circinusX1/exi-ccw/3d/EPTA-BACK.png

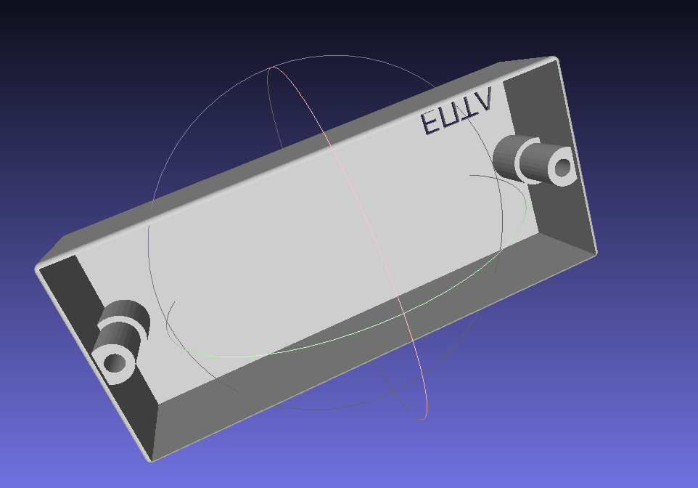
3d/EPTA-BACK.png
