circinusX1/exi-ccw/3d/EPTA-FRONT.png

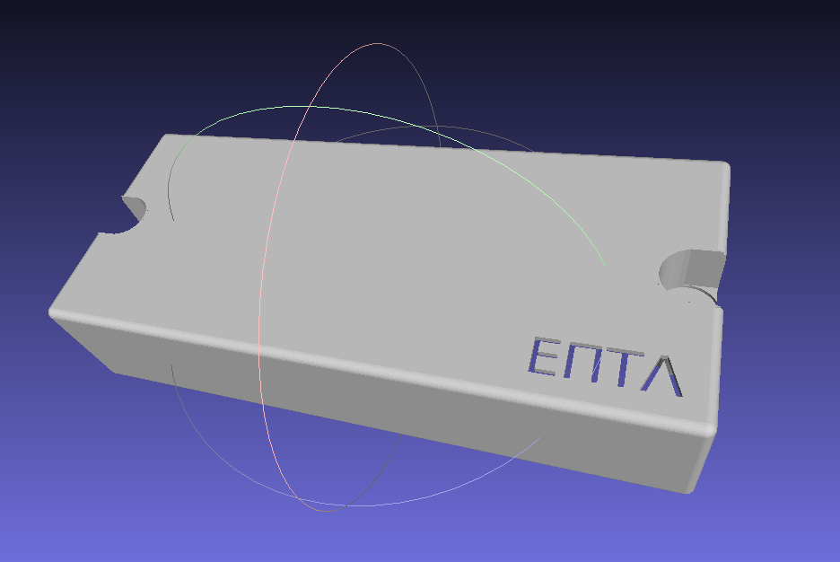
3d/EPTA-FRONT.png
