circinusX1/exi-ccw/3d/EXI-BACK.png

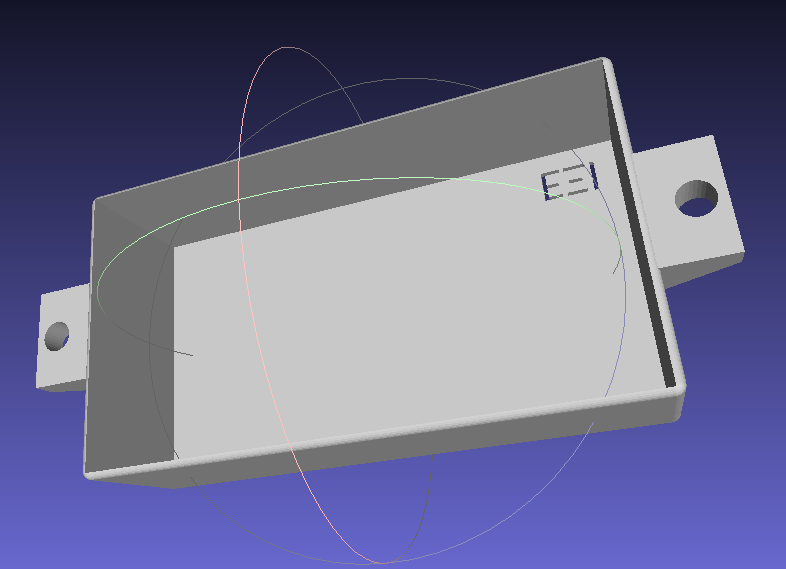
3d/EXI-BACK.png
