circinusX1/exi-ccw/3d/EXI-EPTA-CURA.png

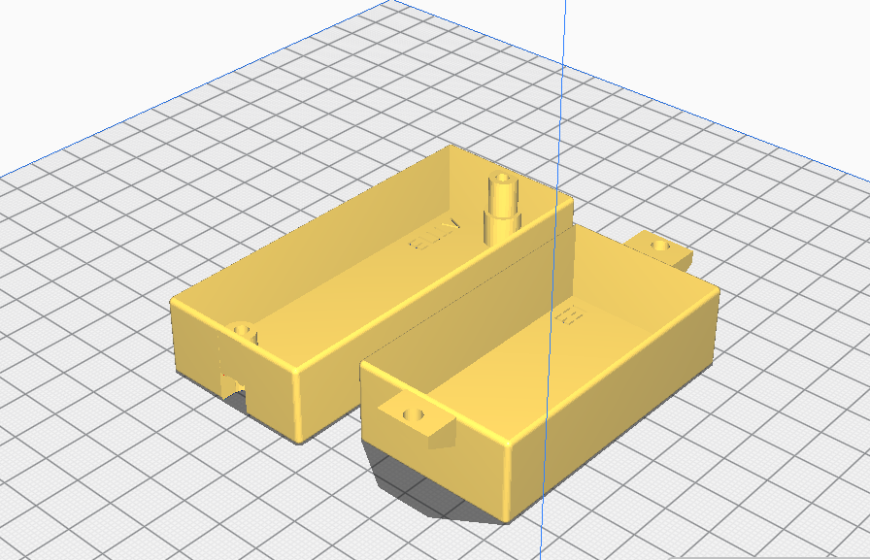
3d/EXI-EPTA-CURA.png
