circinusX1/exi-ccw/3d/EXI-FRONT.png

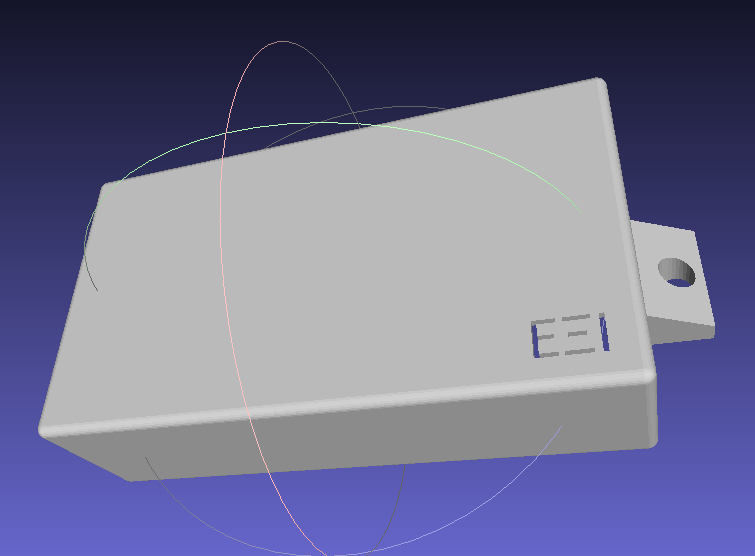
3d/EXI-FRONT.png
