circinusX1/exi-ccw/images/6c-signal.png

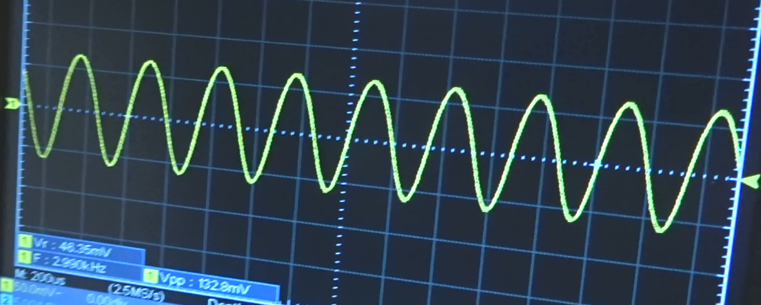
images/6c-signal.png
