circinusX1/exi-ccw/images/chinese-probe.png

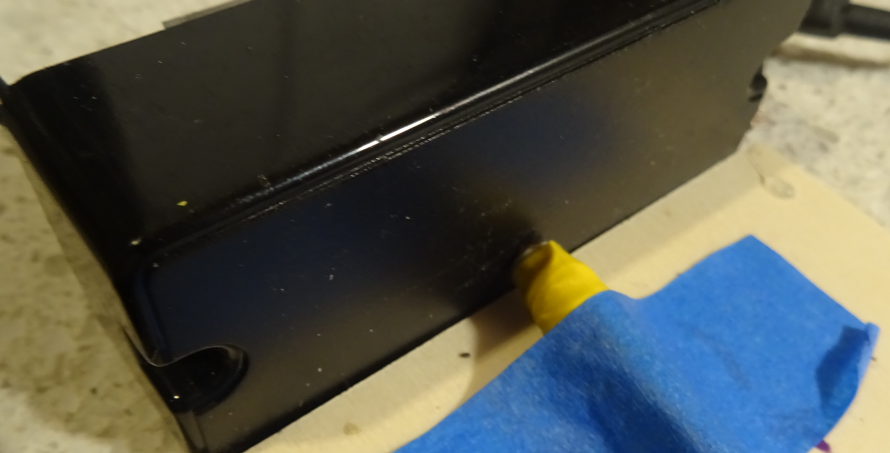
images/chinese-probe.png
