circinusX1/exi-ccw/images/DSC08180.JPG

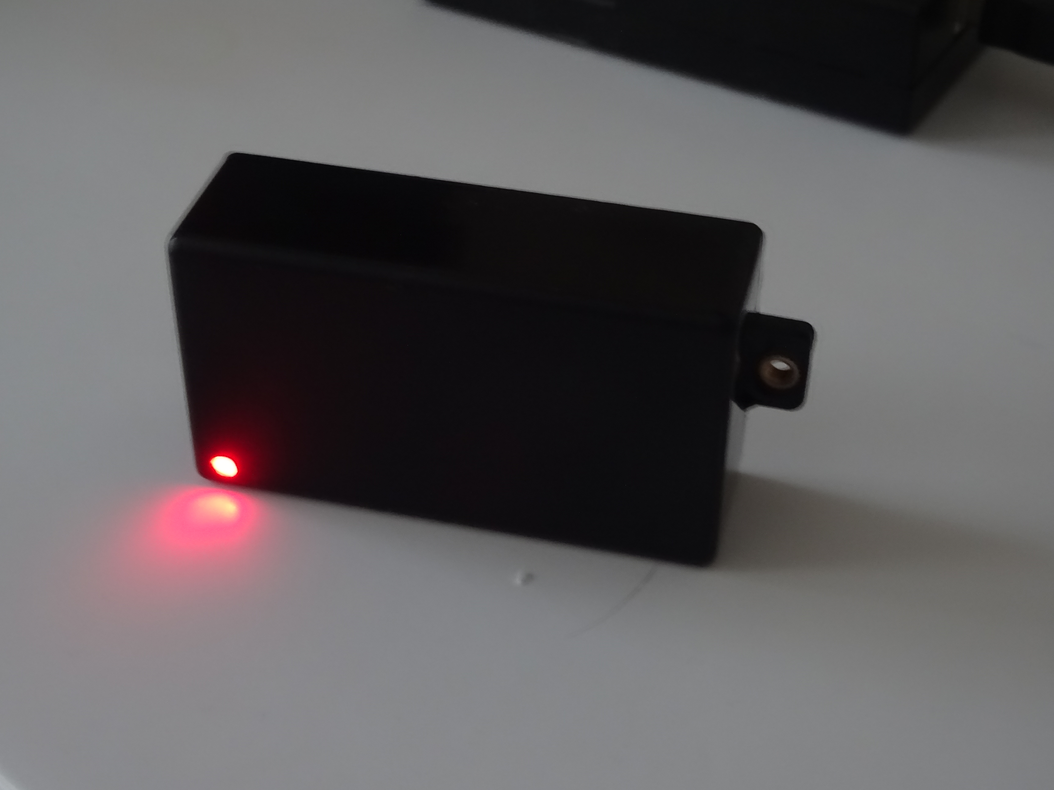
images/DSC08180.JPG
