circinusX1/exi-ccw/images/emg2-probe.png

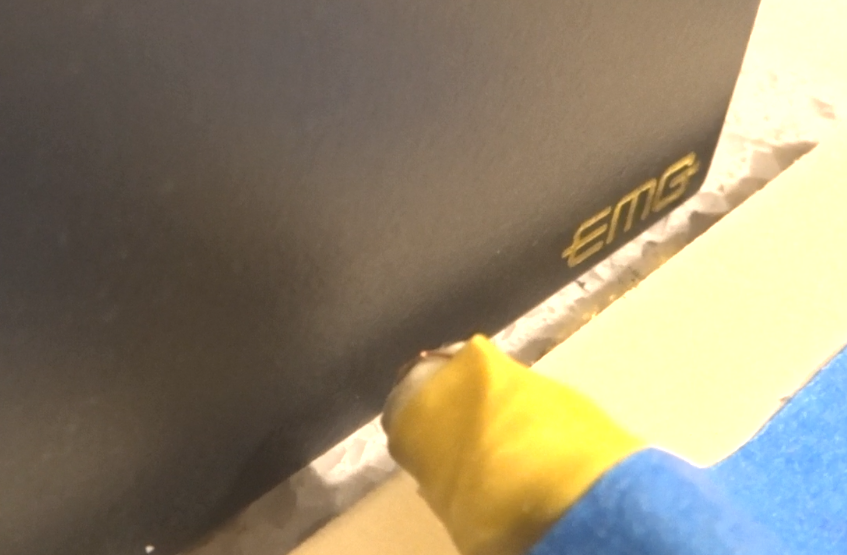
images/emg2-probe.png
