circinusX1/exi-ccw/images/emg-probe.png

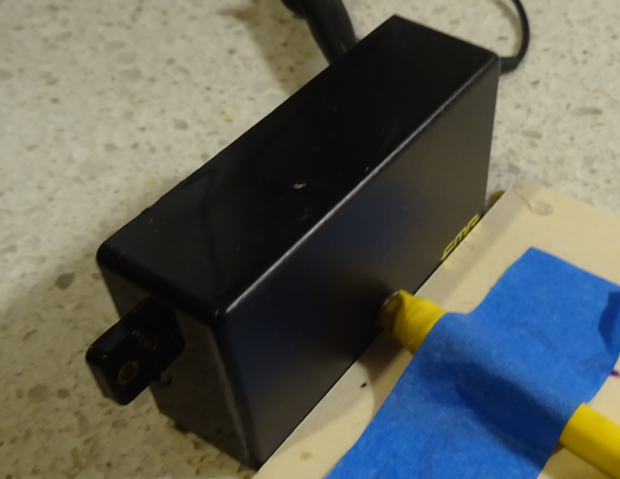
images/emg-probe.png
