circinusX1/exi-ccw/images/frequency-response-guitar-graph.png

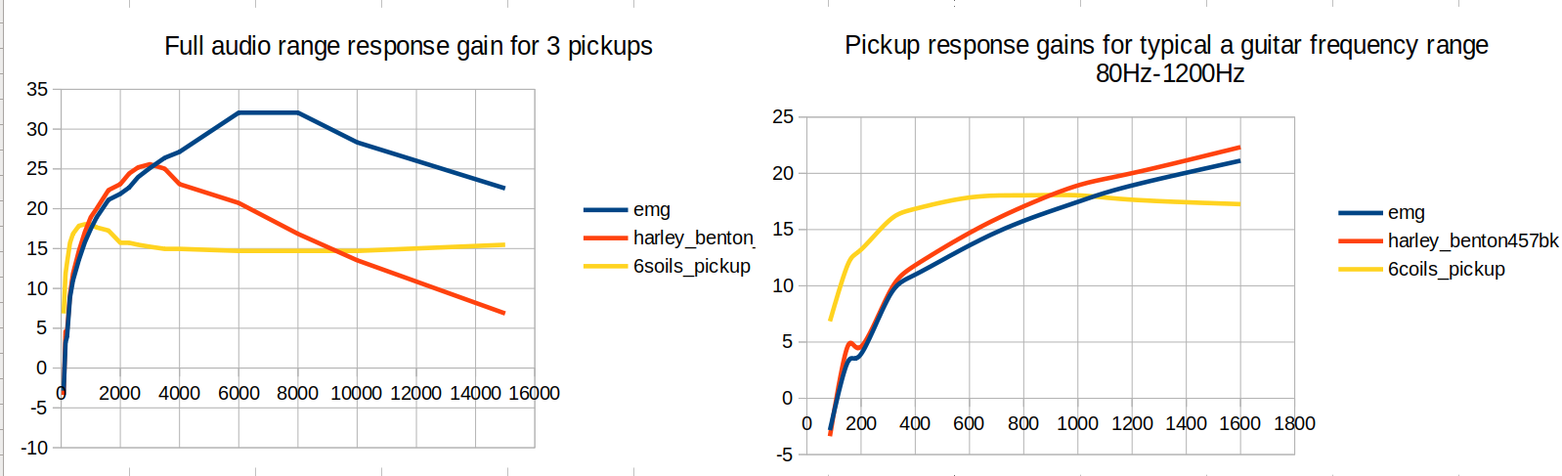
images/frequency-response-guitar-graph.png
