circinusX1/exi-ccw/images/guitar-pickup-interior-blur-blk.png

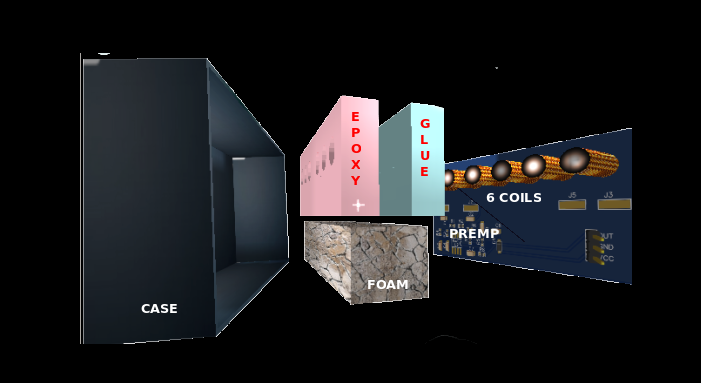
images/guitar-pickup-interior-blur-blk.png
