circinusX1/exi-ccw/images/guitar-pickup-interior-blur.png

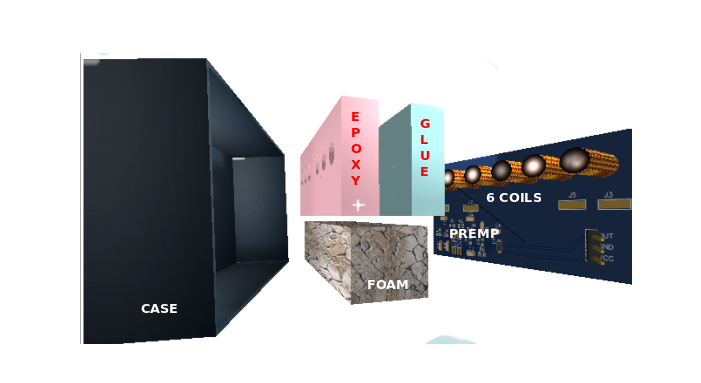
images/guitar-pickup-interior-blur.png
