circinusX1/exi-ccw/images/hum_pickup_schem.png

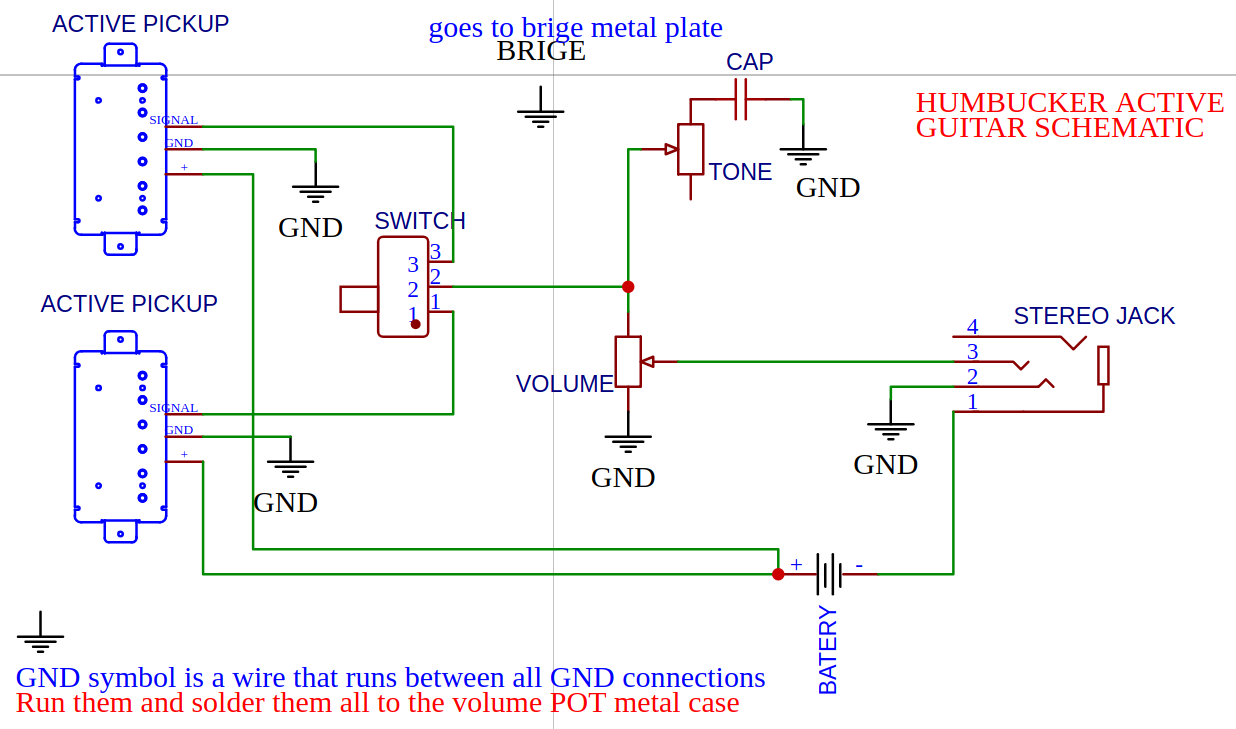
images/hum_pickup_schem.png
