circinusX1/exi-ccw/images/interior-2.png

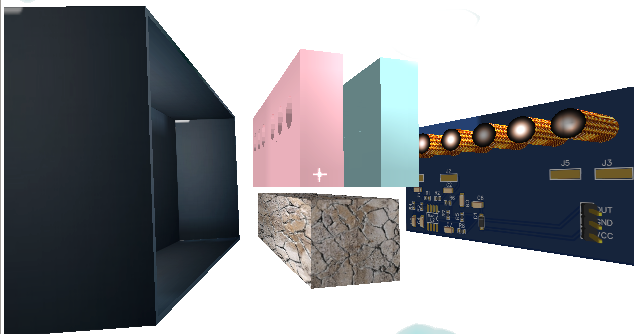
images/interior-2.png
