circinusX1/exi-ccw/images/pick_ccw_1.png

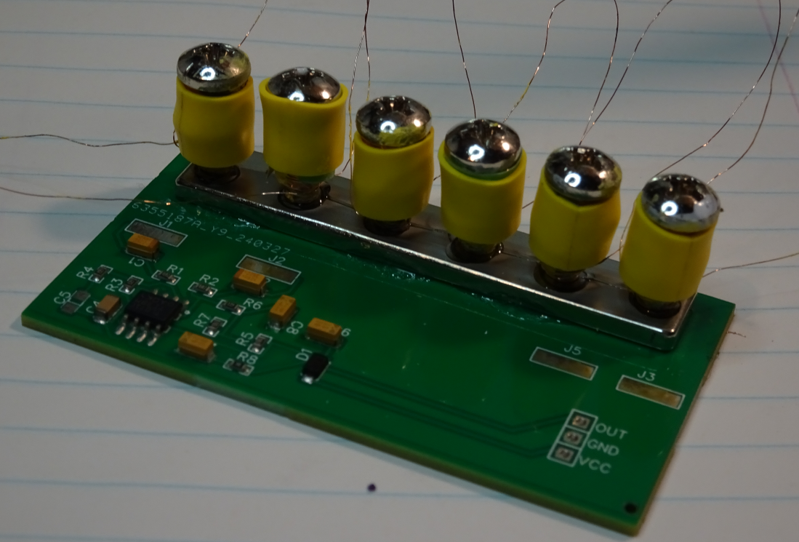
images/pick_ccw_1.png
