circinusX1/exi-ccw/images/pickup-compare-chart.png

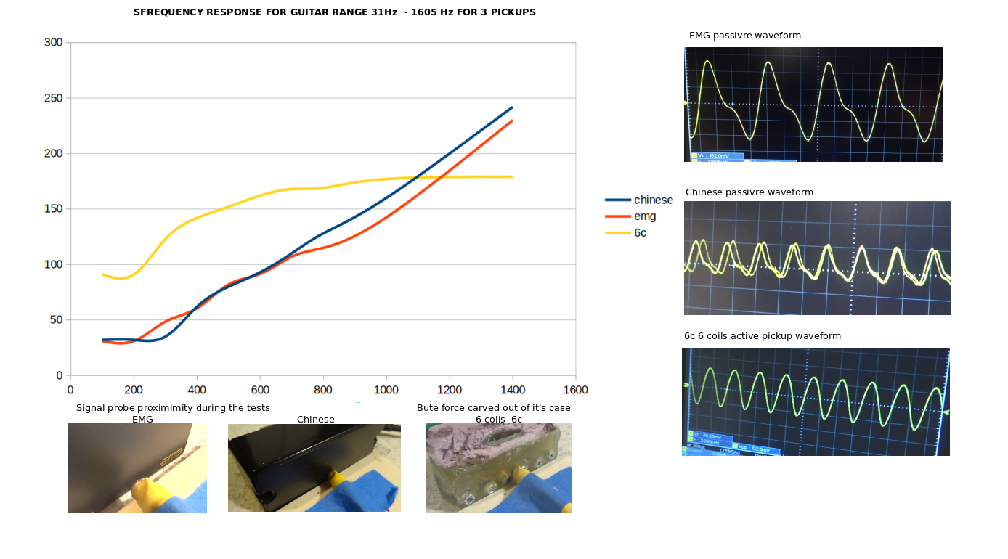
images/pickup-compare-chart.png
