circinusX1/exi-ccw/images/pickup-led.jpg

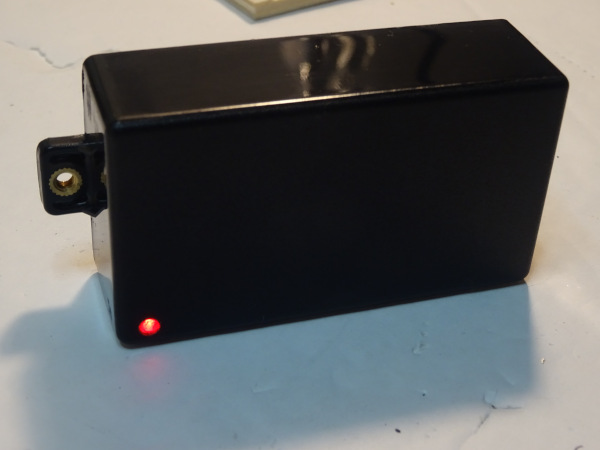
images/pickup-led.jpg
